thebenheckshow/192-tbhs-diycalculator/Documentation/Model C/RPI-CMCDA-V1_1-PUBLIC/GERBERS/RPI-CMCDA-V1_1-PUBLIC-TAS.pdf

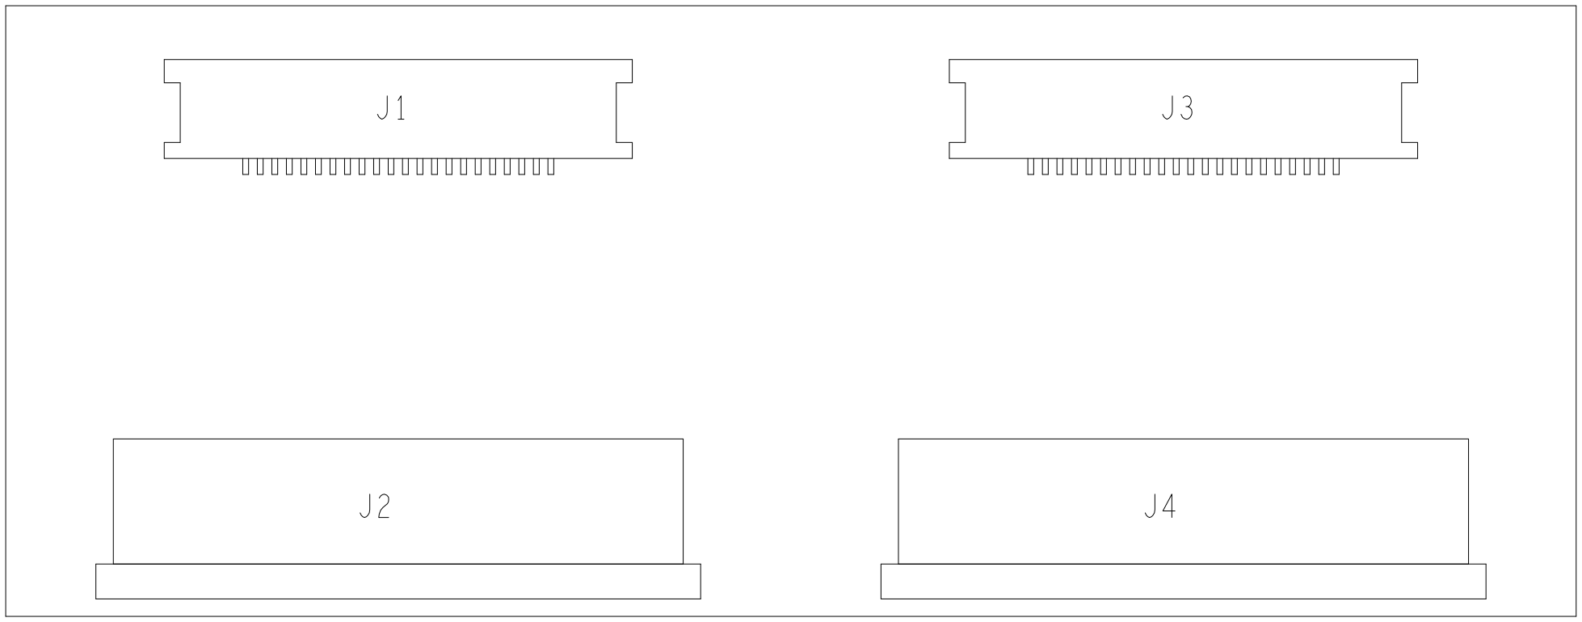
[picture p1: figure]
