thebenheckshow/192-tbhs-diycalculator/Components/Charge Controller/v4/Etch Mask/EtchMask-eagle.png

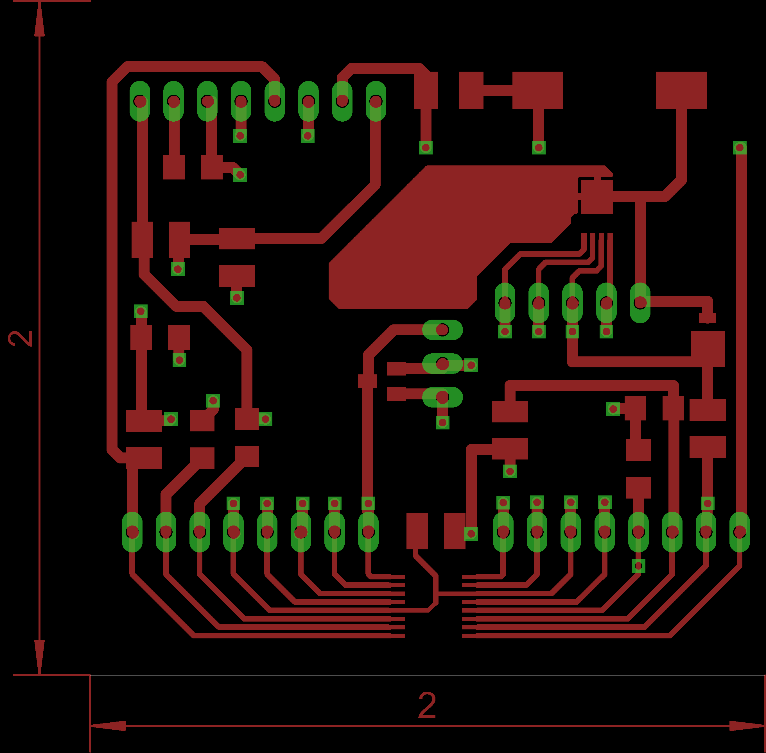
Components/Charge Controller/v4/Etch Mask/EtchMask-eagle.png
