thebenheckshow/192-tbhs-diycalculator/Documentation/Model C/RPI-CMIO-V1_2-PUBLIC/GERBERS/RPI-CMIO-V1_2-PUBLIC-BAS.pdf

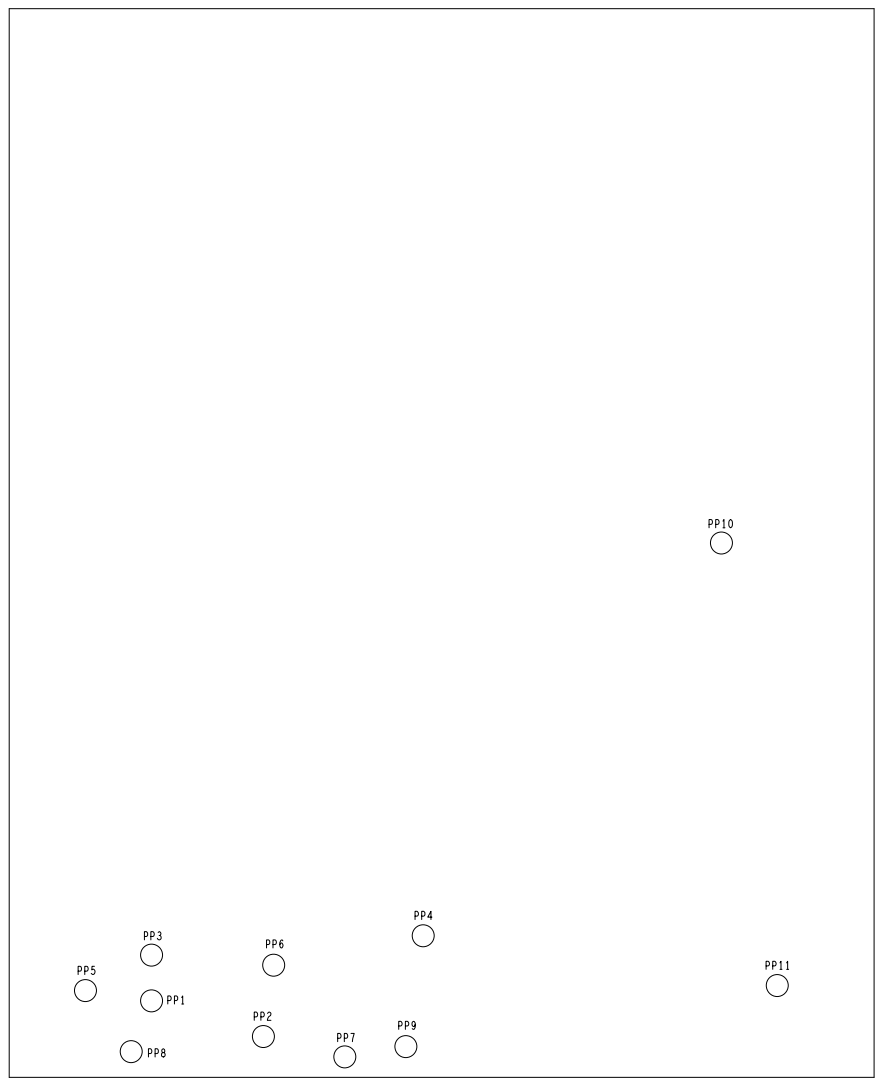
[picture p20: page 1]
