thebenheckshow/192-tbhs-diycalculator/Documentation/Model C/RPI-CMIO-V1_2-PUBLIC/GERBERS/RPI-CMIO-V1_2-PUBLIC-TAS.pdf

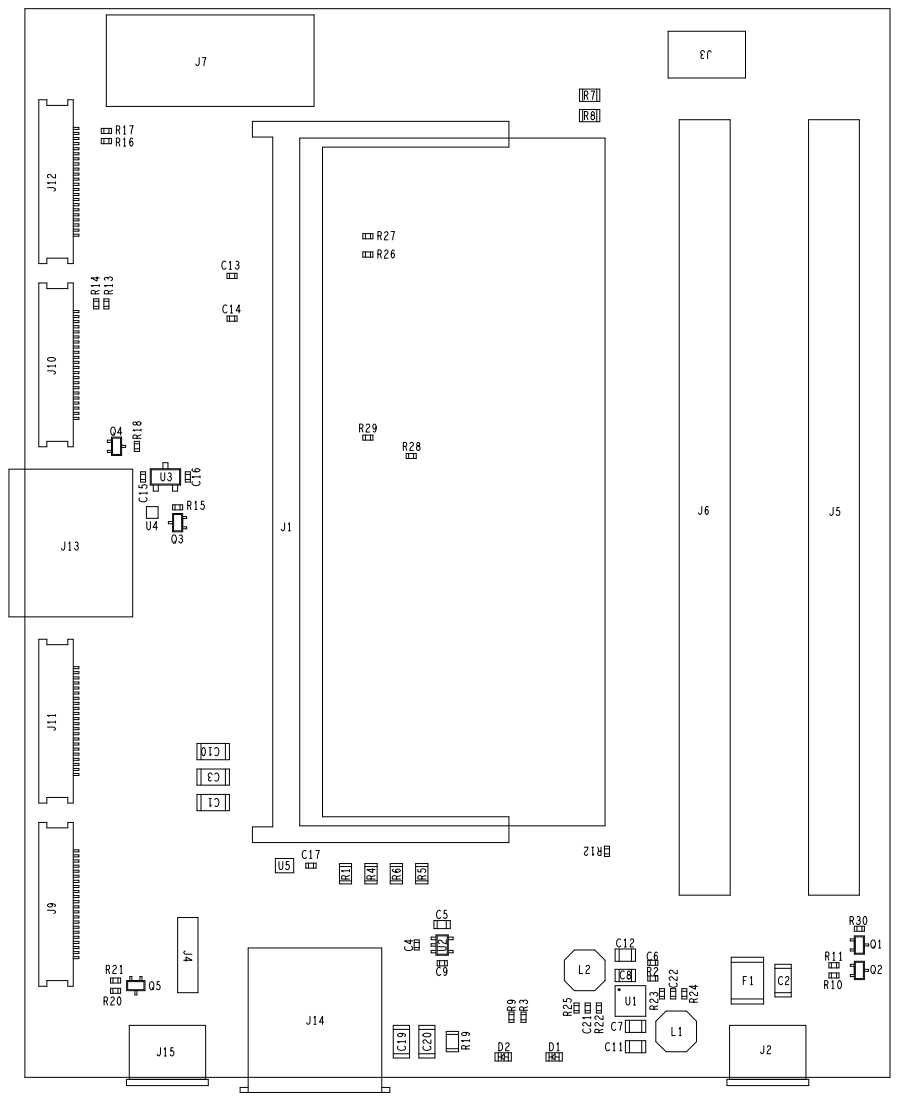
[picture p21: page 1]
